mishave/AlgaeBRIQ/vhausAlageMechanical/3D Files/PCBs/Sensor Board.step

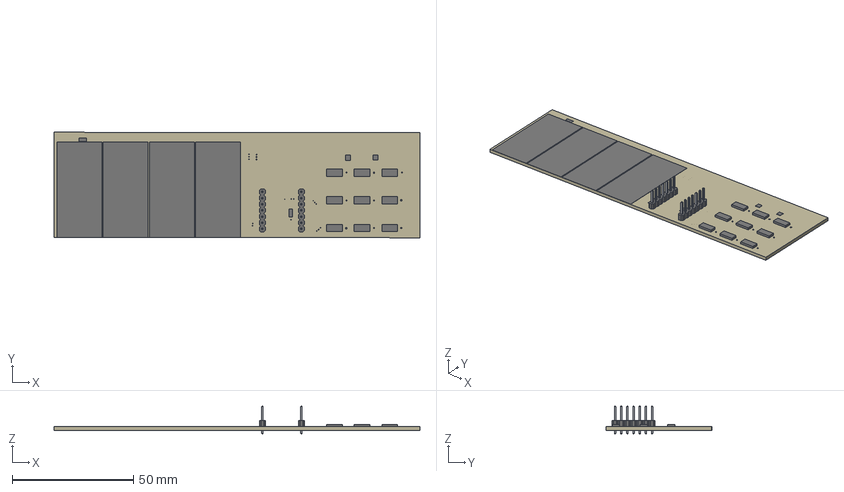
[picture p17: CAD file, 2020-10-28]
vhausAlageMechanical/3D Files/PCBs/Sensor Board.step
150.9 x 43.5 x 11.5 mm
EZO_BOARD x 4
1X01_NO_SILK x 2
PAD.02X.02 x 9
1X07 x 2
