mishave/AlgaeBRIQ/vhausAlageMechanical/3D Files/Punematics/Check Valve.step

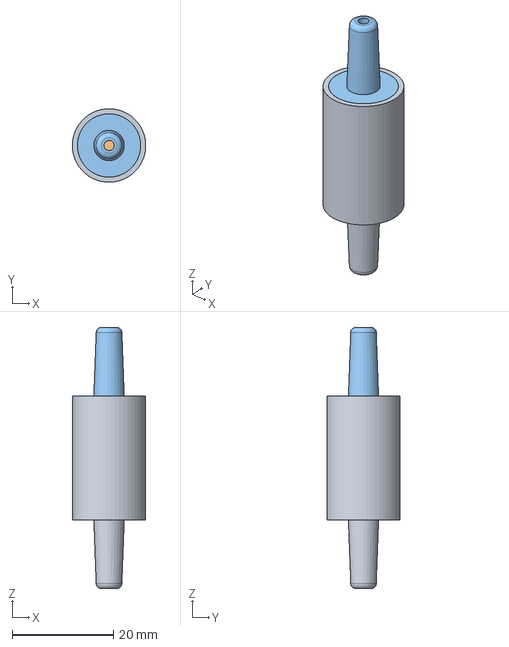
[picture p18: CAD file, 2020-10-28]
vhausAlageMechanical/3D Files/Punematics/Check Valve.step
14.5 x 14.5 x 51.5 mm
