mishave/AlgaeBRIQ/vhausAlageMechanical/3D Files/PVC/DWV PVC Adaptor Male Iron 40mm - Holman.step

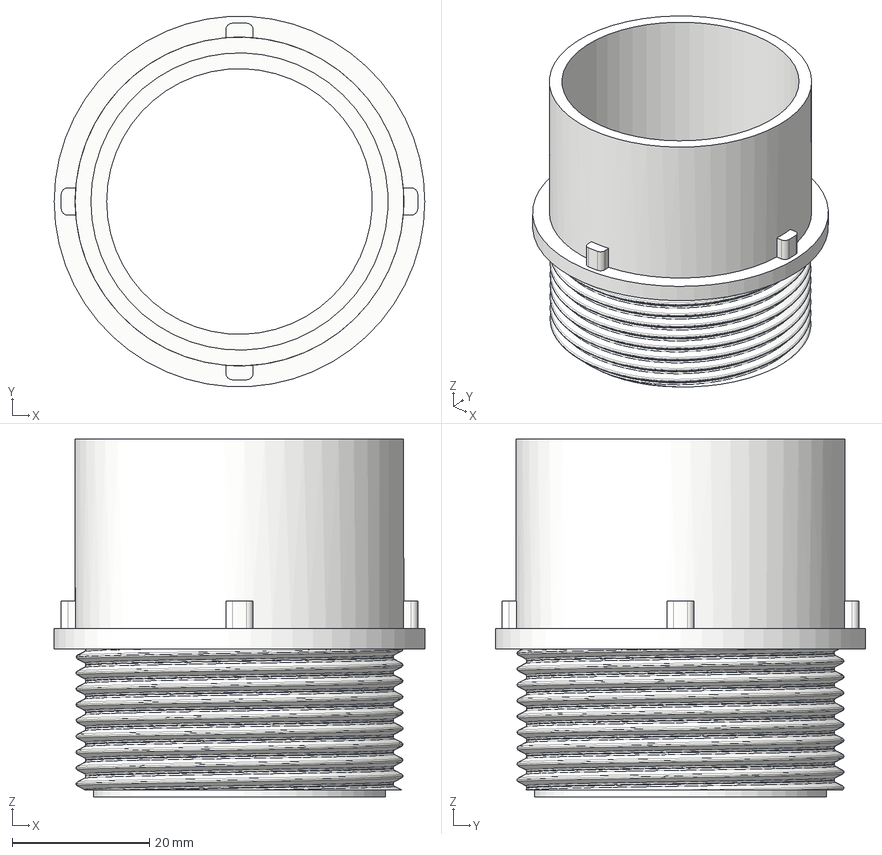
[picture p19: CAD file, 2020-10-28]
vhausAlageMechanical/3D Files/PVC/DWV PVC Adaptor Male Iron 40mm - Holman.step
54.0 x 53.9 x 52.1 mm
