mishave/AlgaeBRIQ/vhausAlageMechanical/3D Files/Servo Motors/PowerHD Servo Horn (Half).step

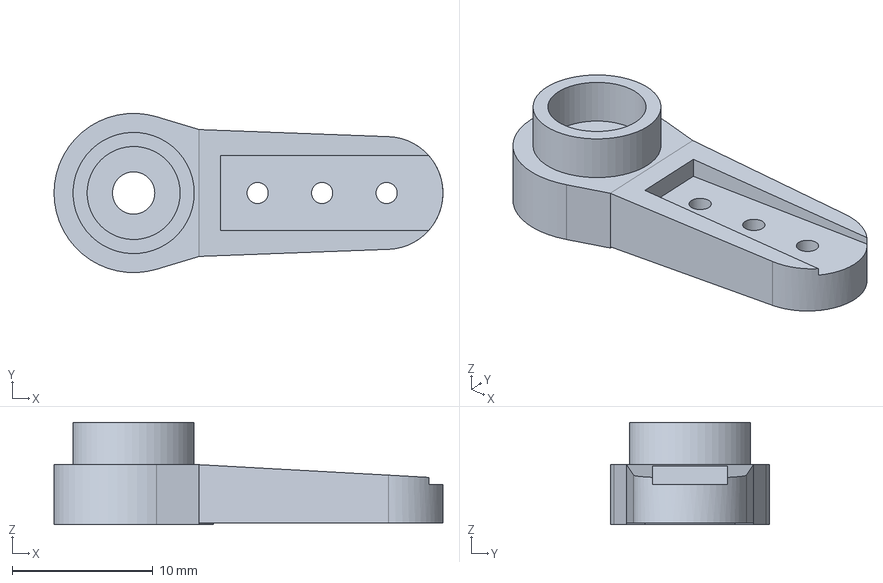
[picture p20: CAD file, 2020-10-28]
vhausAlageMechanical/3D Files/Servo Motors/PowerHD Servo Horn (Half).step
27.6 x 11.3 x 7.25 mm
