mishave/AlgaeBRIQ/vhausAlageMechanical/3D Files/Sub Components/Shut Off Valve Servo Mount.step

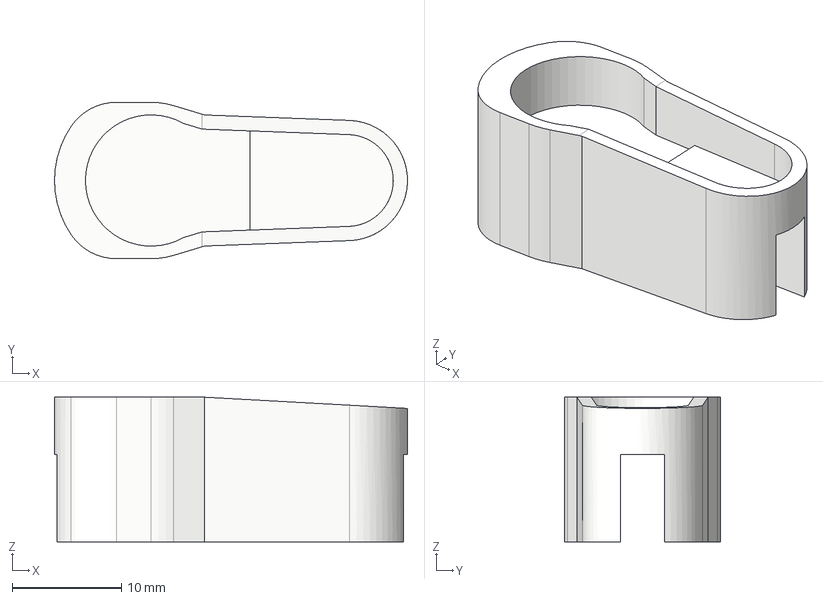
[picture p21: CAD file, 2020-10-28]
vhausAlageMechanical/3D Files/Sub Components/Shut Off Valve Servo Mount.step
32.3 x 14.3 x 13.2 mm
