mishave/AlgaeBRIQ/vhausAlageMechanical/3D Files/Ball Valves/1 2 Two Piece Ball Valve BVS4B L T.step

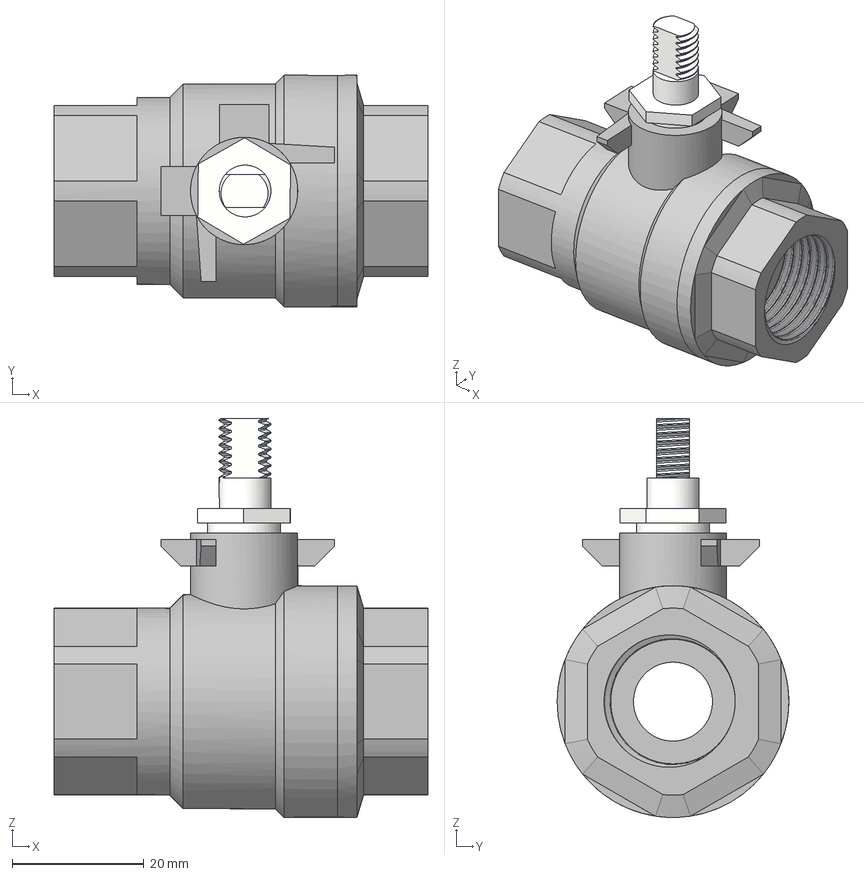
[picture p22: CAD file, 2020-10-28]
vhausAlageMechanical/3D Files/Ball Valves/1 2 Two Piece Ball Valve BVS4B L T.step
56.8 x 35.2 x 60.6 mm
Main Body
2nd Body
