mishave/AlgaeBRIQ/vhausAlageMechanical/3D Files/Electrical/Dosing Pump.step

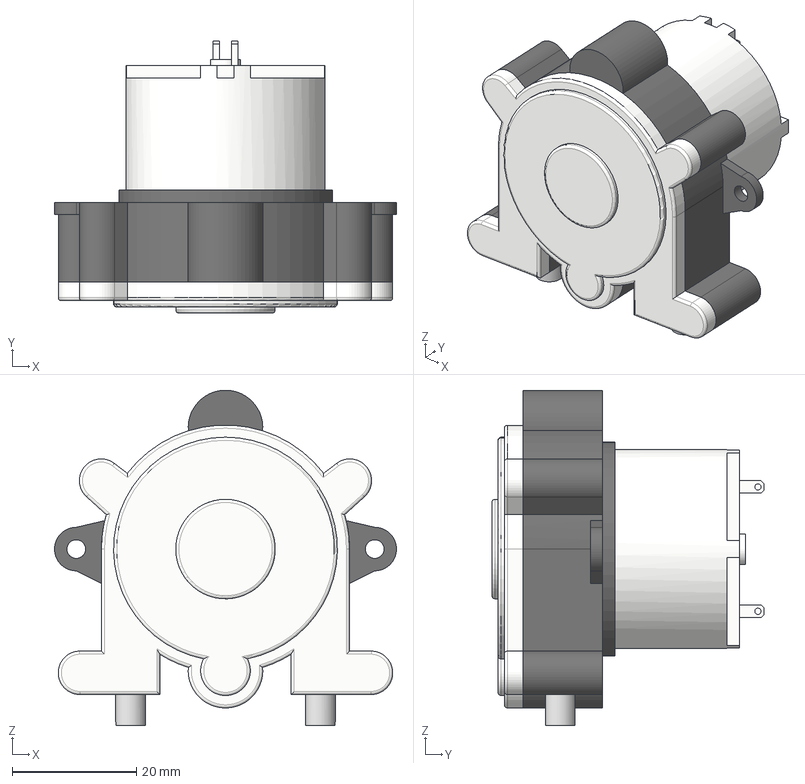
[picture p23: CAD file, 2020-10-28]
vhausAlageMechanical/3D Files/Electrical/Dosing Pump.step
55.0 x 43.8 x 53.9 mm
Motor
base
cover
middle
Tube
