mishave/AlgaeBRIQ/vhausAlageMechanical/3D Files/Punematics/Temp 12 Half Fitting.step

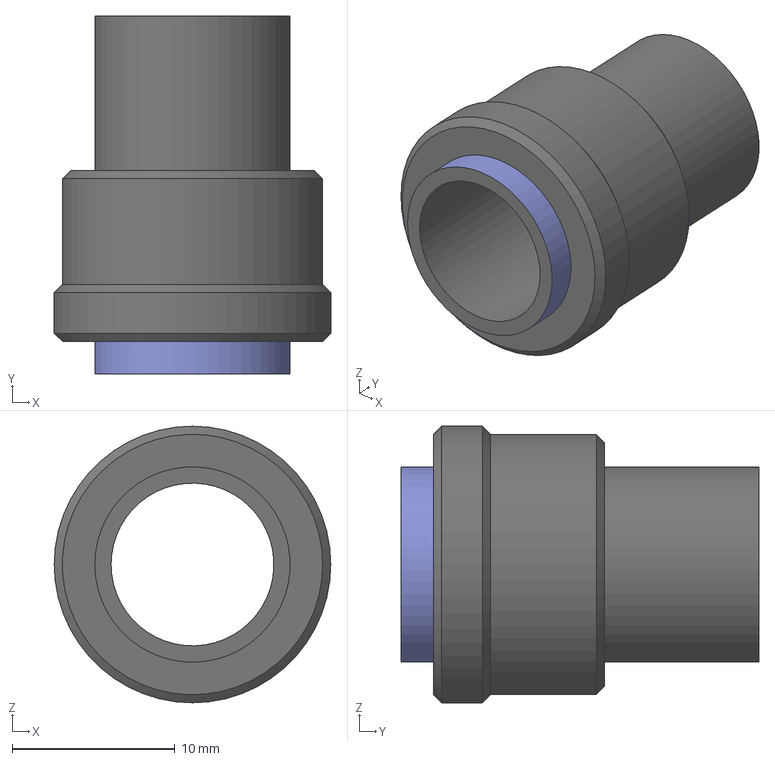
[picture p24: CAD file, 2020-10-28]
vhausAlageMechanical/3D Files/Punematics/Temp 12 Half Fitting.step
17.0 x 22.0 x 17.0 mm
