mishave/AlgaeBRIQ/vhausAlageMechanical/3D Files/PVC/50mm End Cap DWV Holman.step

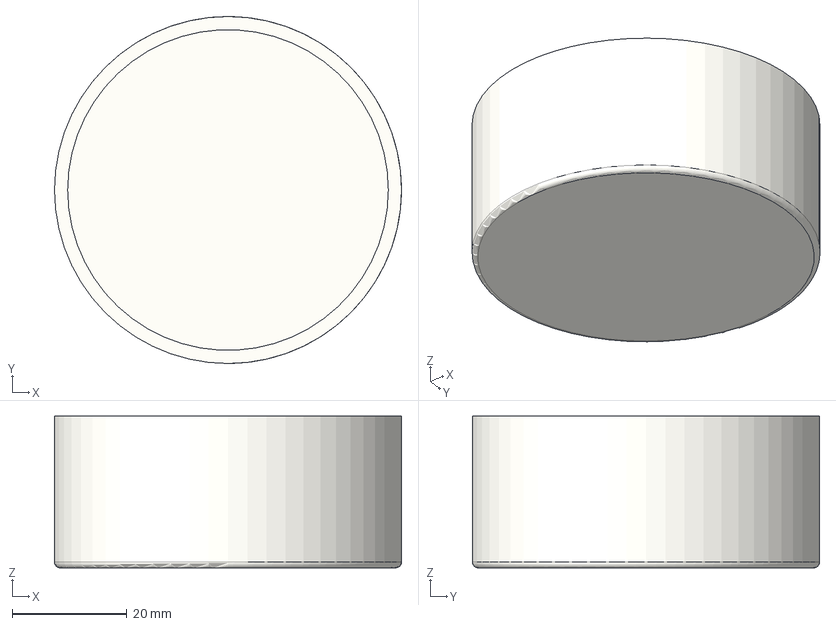
[picture p25: CAD file, 2020-10-28]
vhausAlageMechanical/3D Files/PVC/50mm End Cap DWV Holman.step
60.6 x 60.6 x 26.5 mm
