mishave/AlgaeBRIQ/vhausAlageMechanical/3D Files/Sub Components/Air Box.step

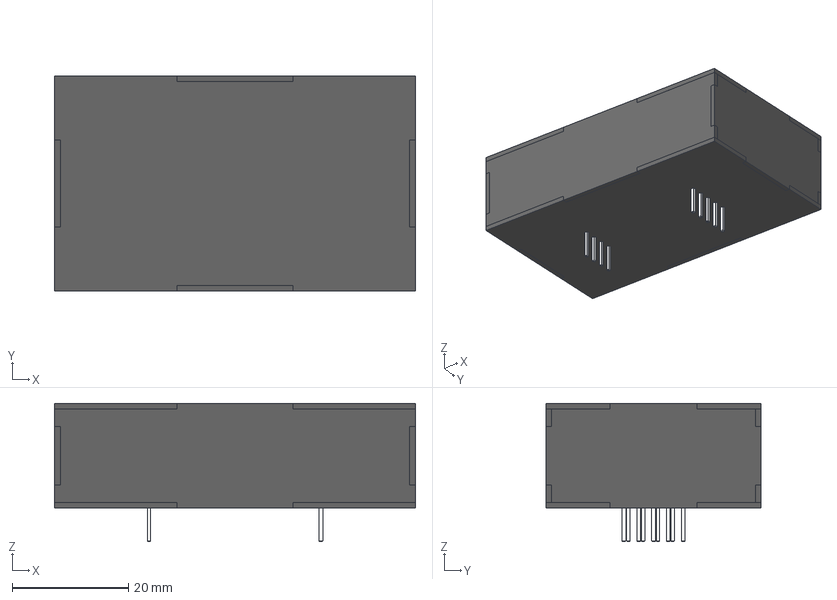
[picture p26: CAD file, 2020-10-28]
vhausAlageMechanical/3D Files/Sub Components/Air Box.step
62.0 x 37.0 x 23.8 mm
spacer
MHZ19B_1
Base
Long Sides
Short Sides
Lid
