mishave/AlgaeBRIQ/vhausAlageMechanical/3D Files/PVC/40mm Short P Trap PVC Caroma U Bend Only.step

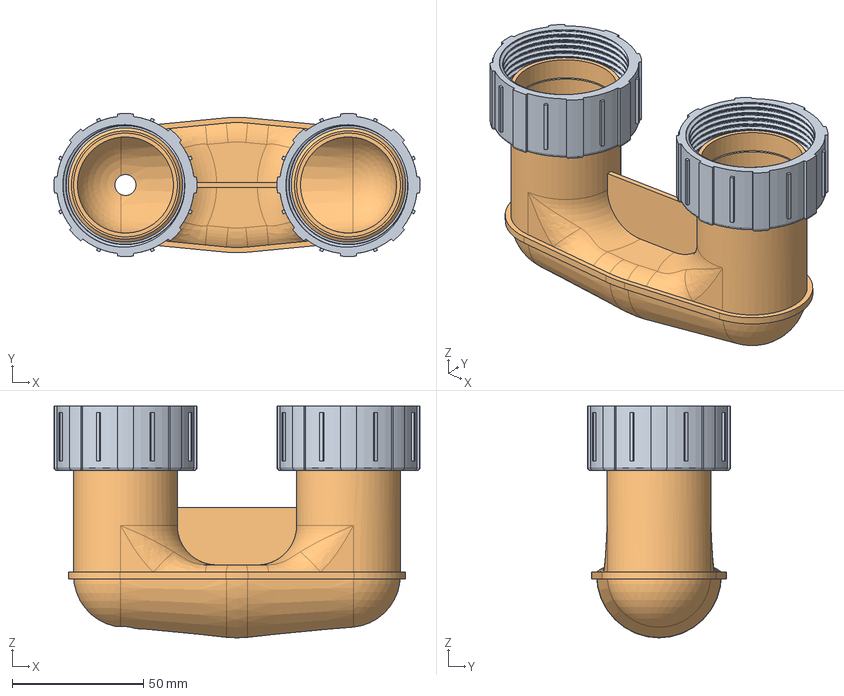
[picture p27: CAD file, 2020-10-28]
vhausAlageMechanical/3D Files/PVC/40mm Short P Trap PVC Caroma U Bend Only.step
139.5 x 54.5 x 88.3 mm
Ring 1
Ring 2
U Bend
