mishave/AlgaeBRIQ/vhausAlageMechanical/3D Files/Sub Components/Heat Transfer.step

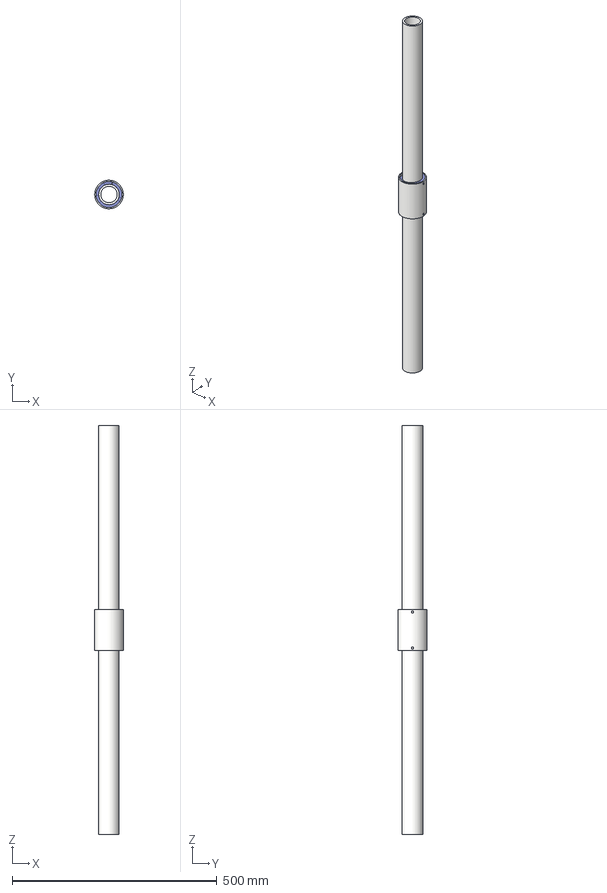
[picture p28: CAD file, 2020-10-28]
vhausAlageMechanical/3D Files/Sub Components/Heat Transfer.step
70.0 x 70.0 x 1000.0 mm
Tube
Pipe
