mishave/AlgaeBRIQ/vhausAlageMechanical/3D Files/PVC/PVT 40mm Holman Tee One Side Cut.step

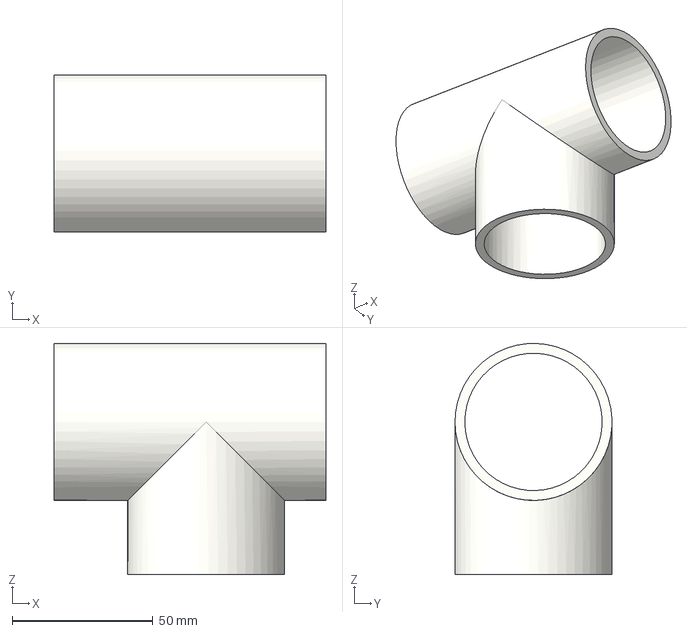
[picture p29: CAD file, 2020-10-28]
vhausAlageMechanical/3D Files/PVC/PVT 40mm Holman Tee One Side Cut.step
96.5 x 55.7 x 82.0 mm
