mishave/AlgaeBRIQ/vhausAlageMechanical/3D Files/Sub Components/Dosing Box.step

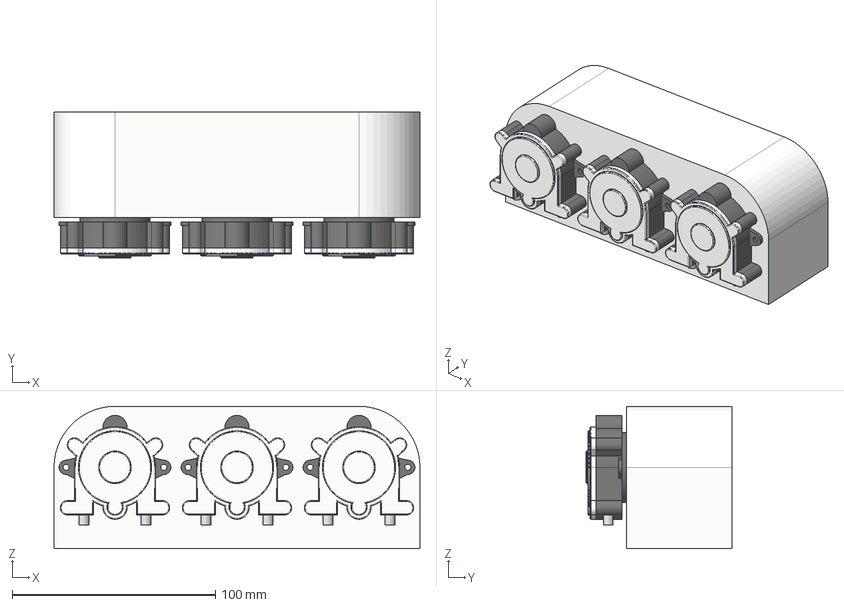
[picture p30: CAD file, 2020-10-28]
vhausAlageMechanical/3D Files/Sub Components/Dosing Box.step
180.0 x 71.8 x 70.0 mm
Motor x 3
base x 3
cover x 3
middle x 3
Tube x 3
