mishave/AlgaeBRIQ/vhausAlageMechanical/3D Files/PVC/20mm Spacer - PVC 40mm Pressure Pipe Spacer.step

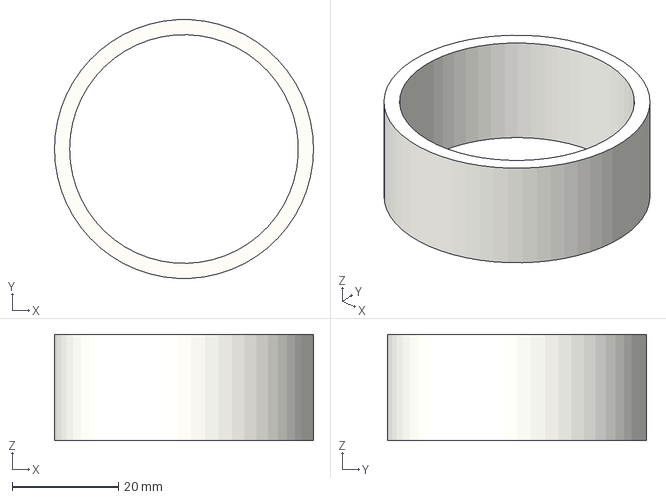
[picture p31: CAD file, 2020-10-28]
vhausAlageMechanical/3D Files/PVC/20mm Spacer - PVC 40mm Pressure Pipe Spacer.step
48.7 x 48.6 x 20.0 mm
