mishave/AlgaeBRIQ/vhausAlageMechanical/3D Files/Sub Components/Harvesting Unit.step

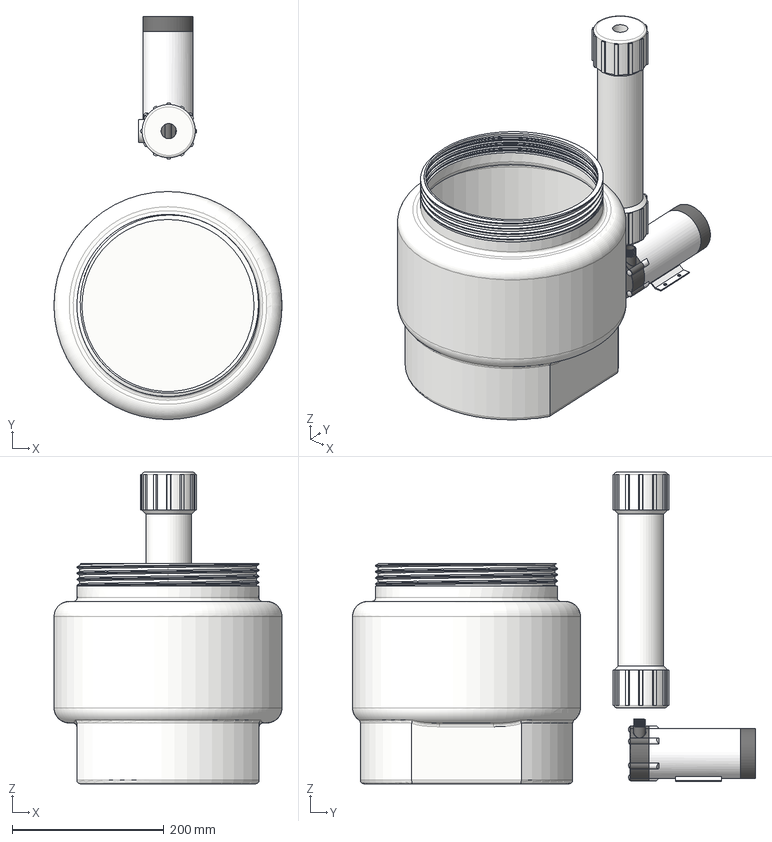
[picture p32: CAD file, 2020-10-28]
vhausAlageMechanical/3D Files/Sub Components/Harvesting Unit.step
300.0 x 530.3 x 410.0 mm
Haarvest Pump
Tank
Cross Flow Filter
