mishave/AlgaeBRIQ/vhausAlageMechanical/3D Files/PVC/40mm DWV female Holman.step

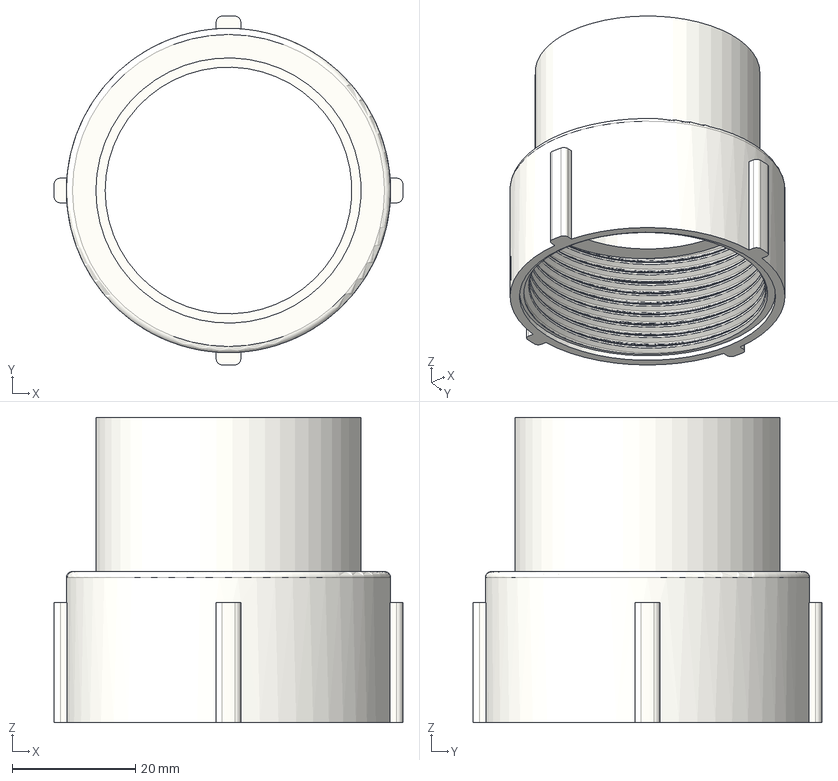
[picture p33: CAD file, 2020-10-28]
vhausAlageMechanical/3D Files/PVC/40mm DWV female Holman.step
56.6 x 56.6 x 49.5 mm
