mishave/AlgaeBRIQ/vhausAlageMechanical/3D Files/Sub Components/Tube Coupling.step

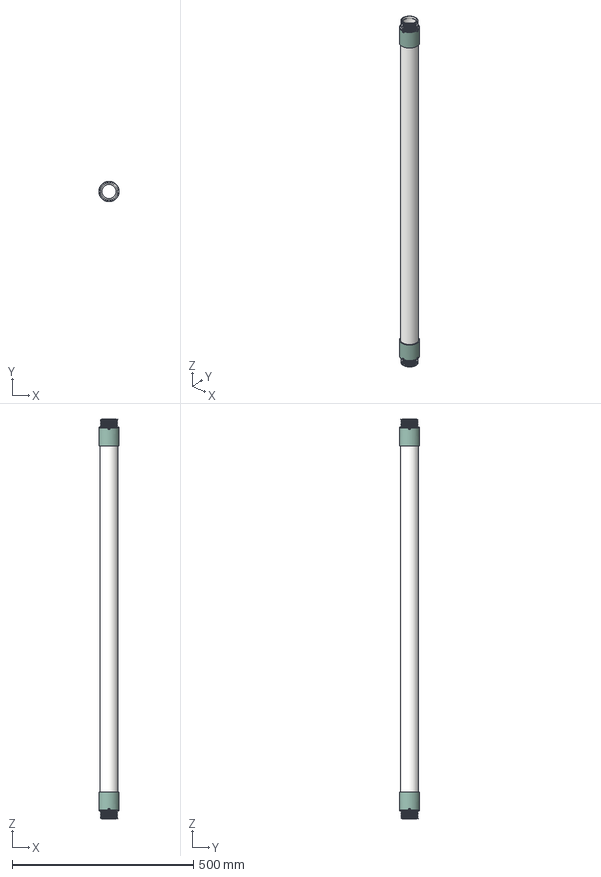
[picture p34: CAD file, 2020-10-28]
vhausAlageMechanical/3D Files/Sub Components/Tube Coupling.step
56.2 x 56.2 x 1103.6 mm
Coupling 1
Coupling 2
Tube
PVC x 2
