mishave/AlgaeBRIQ/vhausAlageMechanical/3D Files/PVC/PVT 40mm Holman Tee Both Sides Cut.step

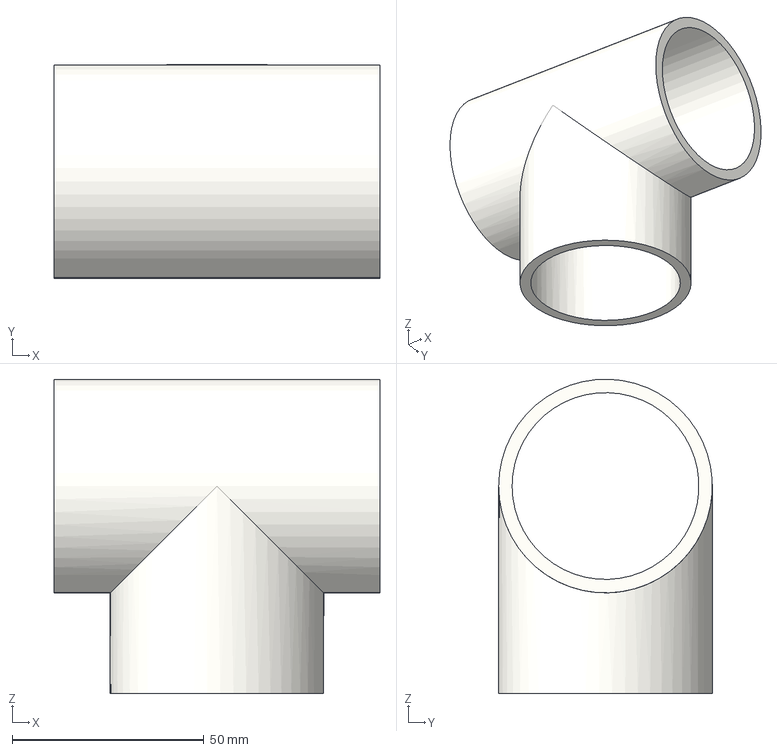
[picture p35: CAD file, 2020-10-28]
vhausAlageMechanical/3D Files/PVC/PVT 40mm Holman Tee Both Sides Cut.step
85.0 x 55.7 x 82.0 mm
