mishave/AlgaeBRIQ/vhausAlageMechanical/3D Files/Sub Components/3 8 Flow Control Valve.step

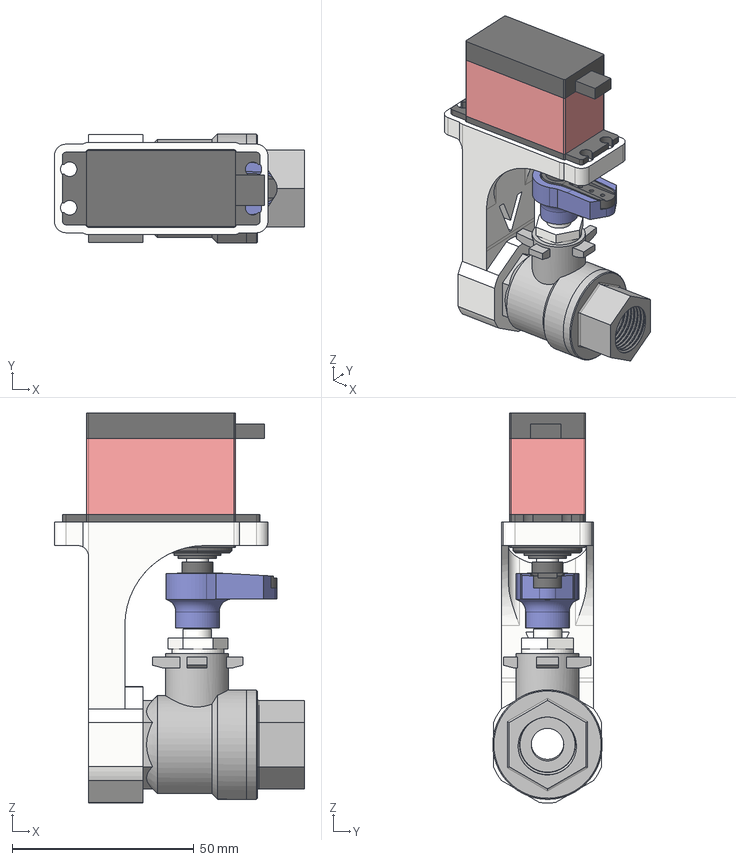
[picture p36: CAD file, 2020-10-28]
vhausAlageMechanical/3D Files/Sub Components/3 8 Flow Control Valve.step
68.9 x 30.1 x 107.4 mm
Servo 20Kg
Single Horn
3/8 Two Piece Ball Valve BVS3B-L-T
valve
Horn Seat
Main Body
